zeekey85/LabStack-Rack/images/hybrid3.png

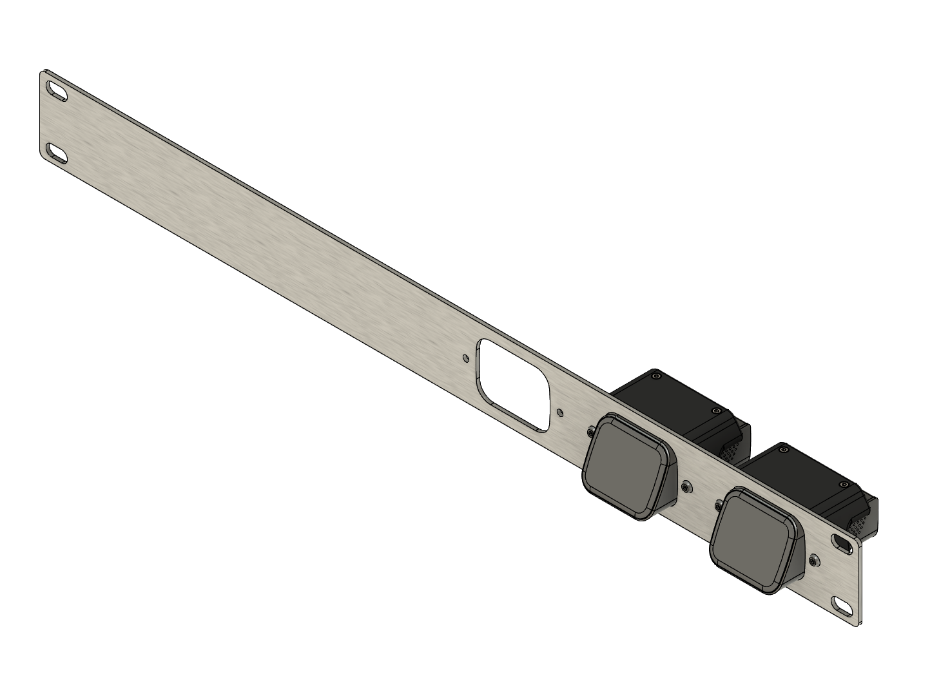
images/hybrid3.png
