zeekey85/LabStack-Rack/images/hybrid4.png

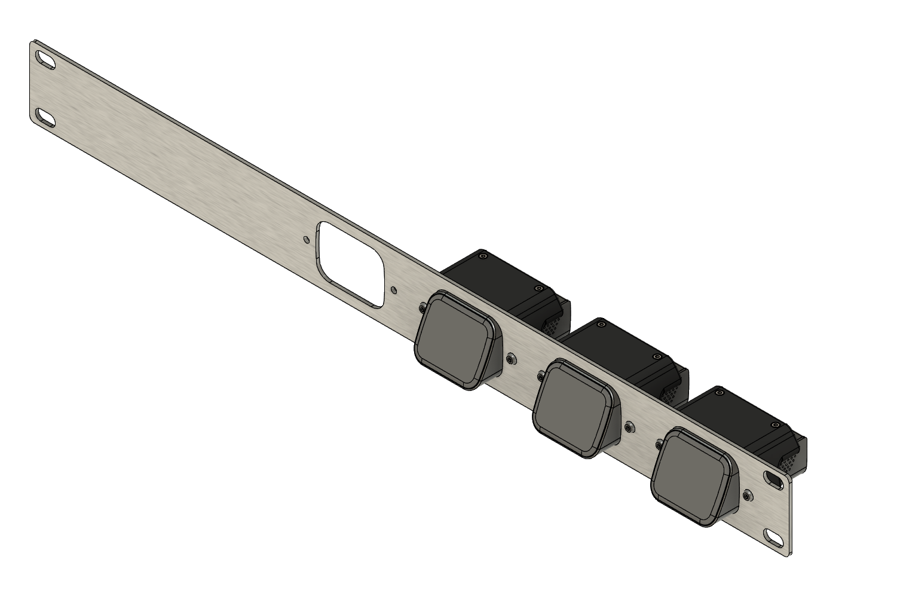
images/hybrid4.png
