zeekey85/LabStack-Rack/images/hybridshort2.png

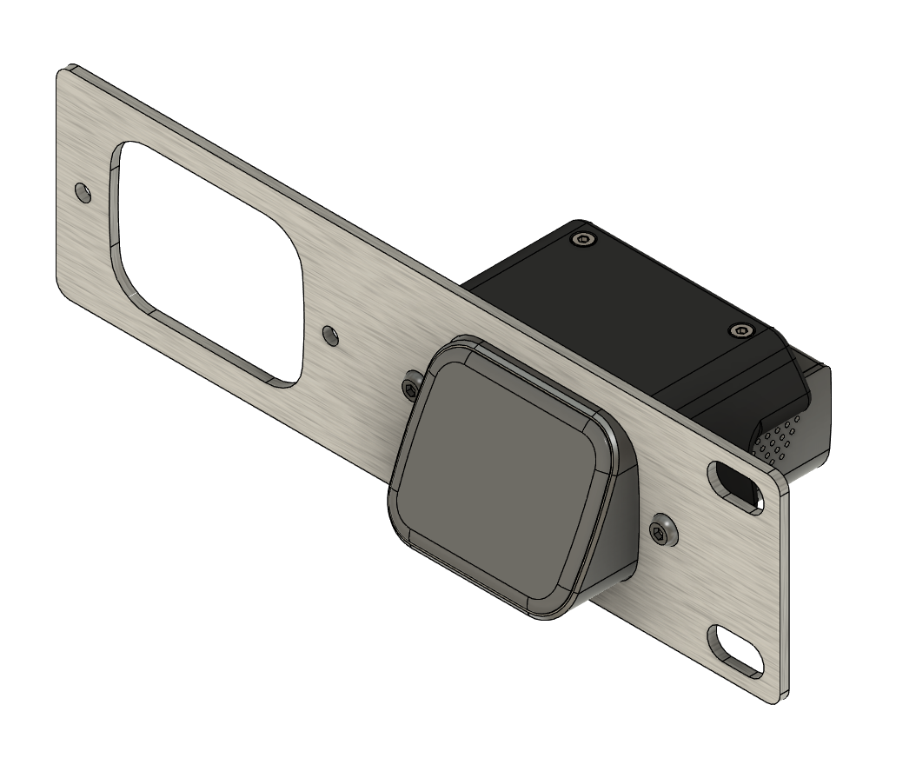
images/hybridshort2.png
