zeekey85/LabStack-Rack/LabStack Rack Mini/STLs/1U Mini Drawer Insert.stl

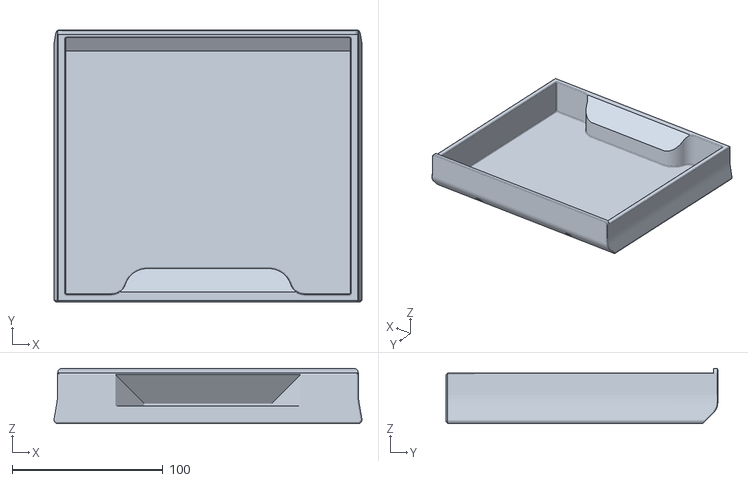
[picture p27: CAD file, 2025-01-28]
LabStack Rack Mini/STLs/1U Mini Drawer Insert.stl
204.1 x 180.0 x 36.7
