zeekey85/LabStack-Rack/full3d/1x Module 6x Keystone Left.stl

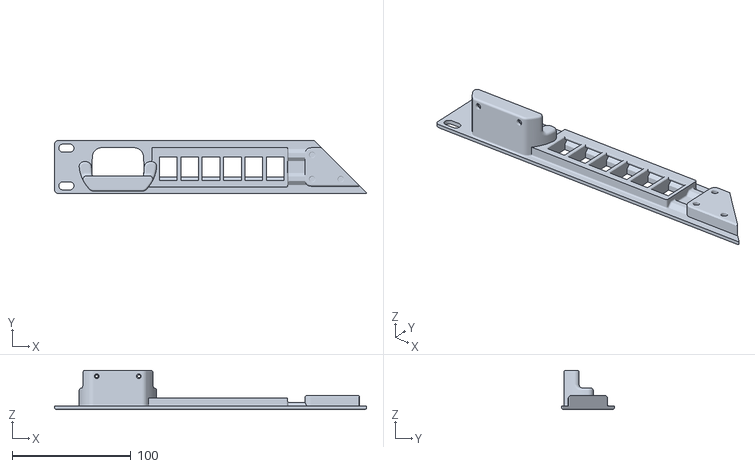
[picture p28: CAD file, 2025-01-24]
full3d/1x Module 6x Keystone Left.stl
262.8 x 44.4 x 33.2
