zeekey85/LabStack-Rack/hybrid/JetKVM 1U 2-Module.dxf

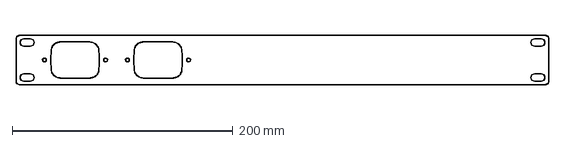
[picture p29: CAD file, 2024-12-10]
hybrid/JetKVM 1U 2-Module.dxf
482.6 x 44.5 mm
