zeekey85/LabStack-Rack/LabStack Rack Mini/STLs/1U Mini HomeAssistant Yellow.stl

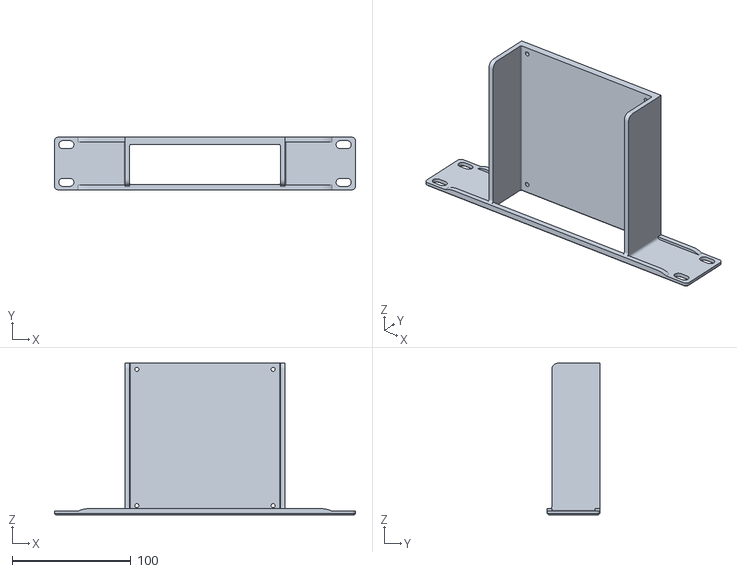
[picture p30: CAD file, 2025-01-26]
LabStack Rack Mini/STLs/1U Mini HomeAssistant Yellow.stl
254.0 x 44.4 x 128.0
