zeekey85/LabStack-Rack/LabStack Rack Mini/STLs/1U Mini Add HomeAssistant Yellow Spacer x4.stl

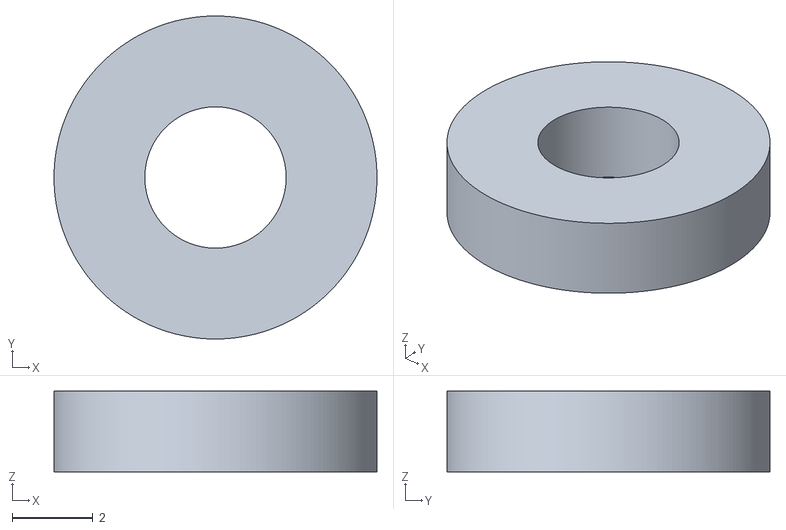
[picture p32: CAD file, 2025-01-26]
LabStack Rack Mini/STLs/1U Mini Add HomeAssistant Yellow Spacer x4.stl
8.00 x 8.00 x 2.00
