zeekey85/LabStack-Rack/full3d/2x Modules Short Right Mount.stl

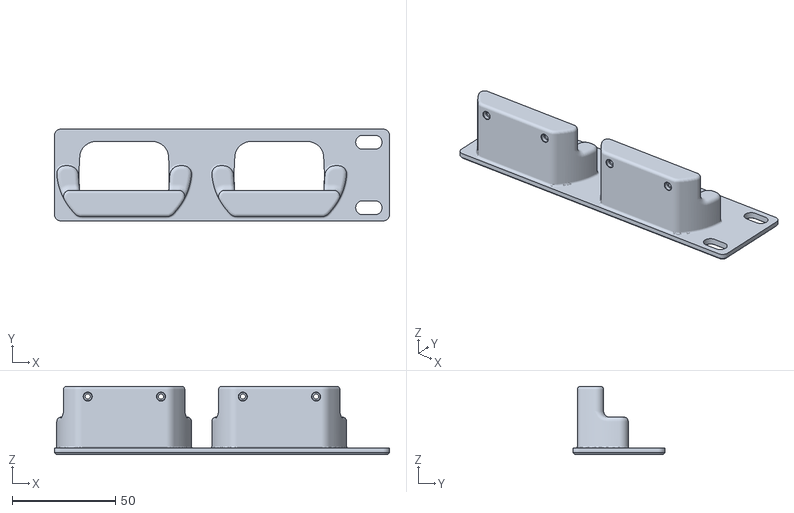
[picture p33: CAD file, 2025-01-09]
full3d/2x Modules Short Right Mount.stl
162.3 x 44.4 x 33.2
