zeekey85/LabStack-Rack/LabStack Rack Mini/STLs/1U Mini Drawer Base.stl

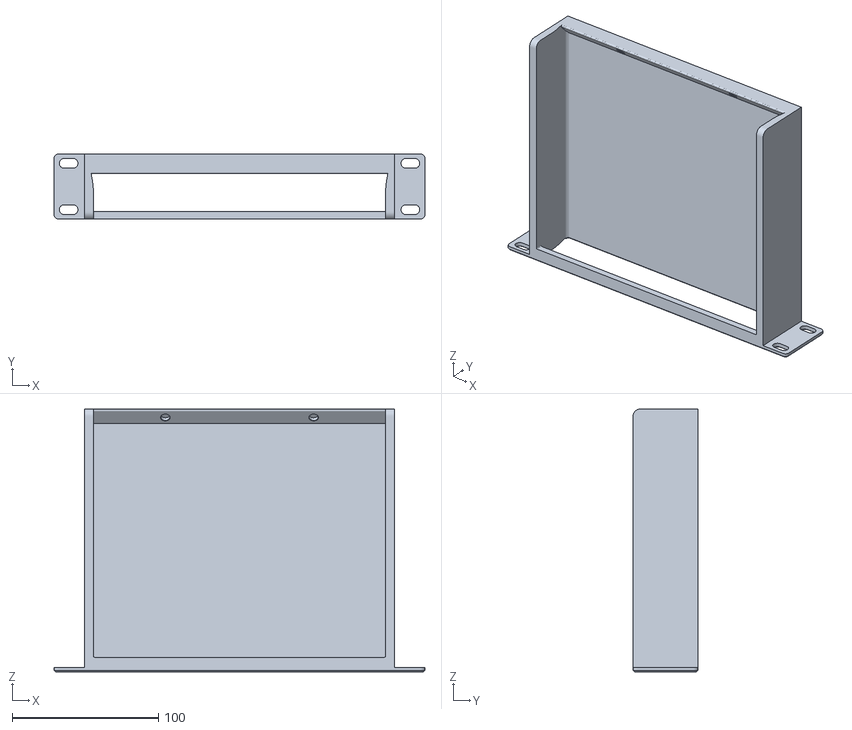
[picture p35: CAD file, 2025-01-26]
LabStack Rack Mini/STLs/1U Mini Drawer Base.stl
254.0 x 44.4 x 180.0
