zeekey85/LabStack-Rack/full3d/1x Module Right.stl

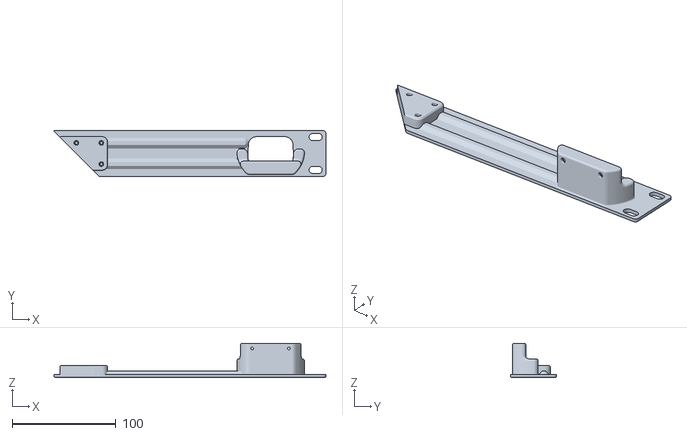
[picture p36: CAD file, 2024-12-17]
full3d/1x Module Right.stl
262.8 x 44.4 x 33.2
