zeekey85/LabStack-Rack/hybrid/JetKVM 1U 1-Module Short.dxf

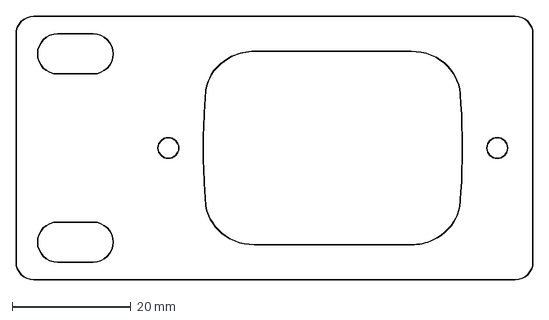
[picture p37: CAD file, 2024-12-10]
hybrid/JetKVM 1U 1-Module Short.dxf
87.2 x 44.5 mm
