zeekey85/LabStack-Rack/full3d/1x Module Short Left Mount.stl

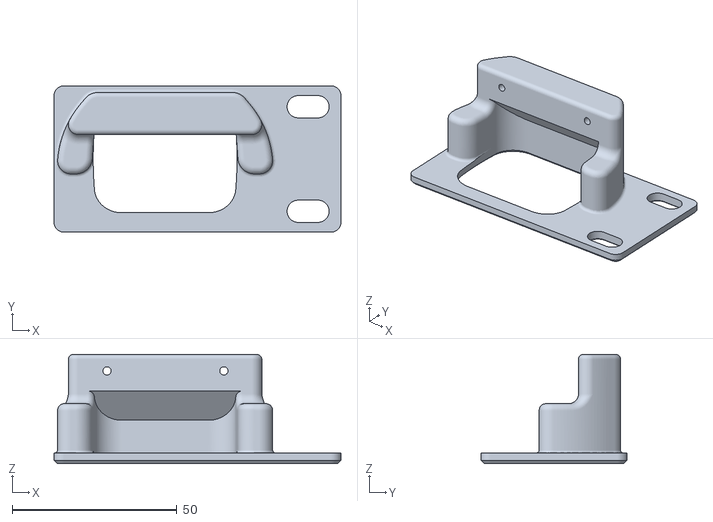
[picture p38: CAD file, 2024-12-17]
full3d/1x Module Short Left Mount.stl
87.2 x 44.5 x 33.2
