zeekey85/LabStack-Rack/hybrid/JetKVM 1U 3-Module.dxf

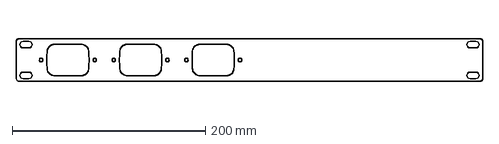
[picture p40: CAD file, 2024-12-10]
hybrid/JetKVM 1U 3-Module.dxf
482.6 x 44.5 mm
