zeekey85/LabStack-Rack/hybrid/JetKVM 1U 2-Module Short.dxf

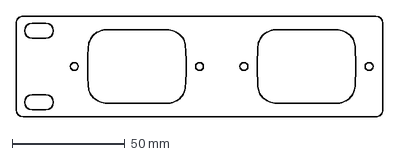
[picture p41: CAD file, 2024-12-10]
hybrid/JetKVM 1U 2-Module Short.dxf
162.3 x 44.5 mm
