zeekey85/LabStack-Rack/full3d/3x Modules 10in Single.stl

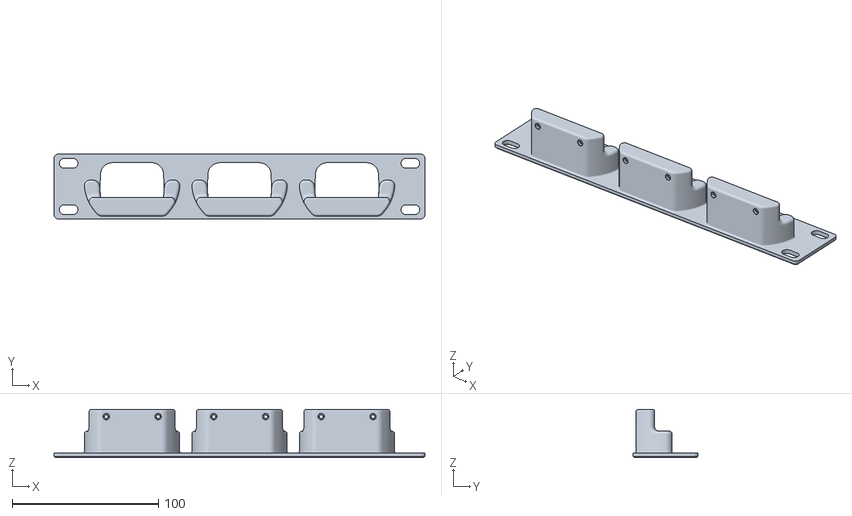
[picture p42: CAD file, 2024-12-17]
full3d/3x Modules 10in Single.stl
254.0 x 44.4 x 33.2
