zeekey85/LabStack-Rack/full3d/Brace.stl

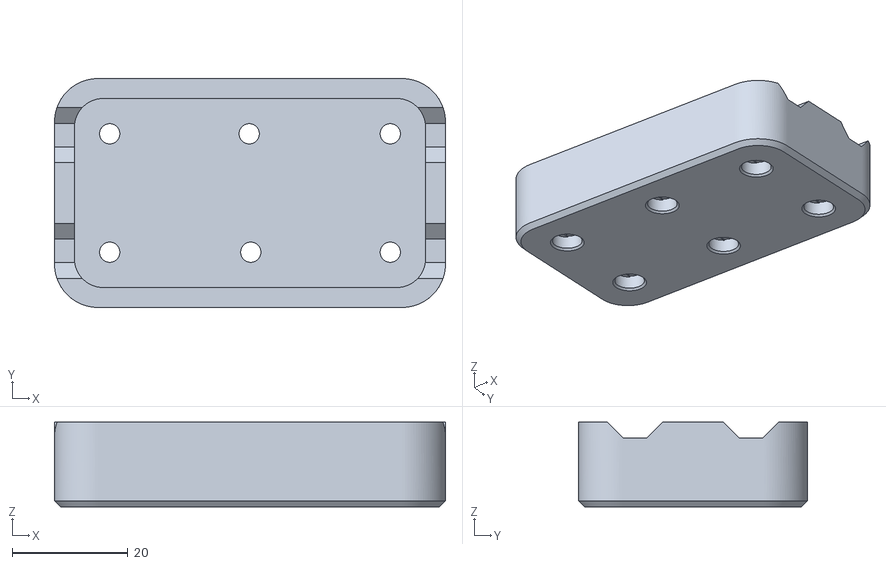
[picture p43: CAD file, 2024-12-17]
full3d/Brace.stl
67.5 x 39.5 x 14.6
