zeekey85/LabStack-Rack/full3d/Blank Module Right.stl

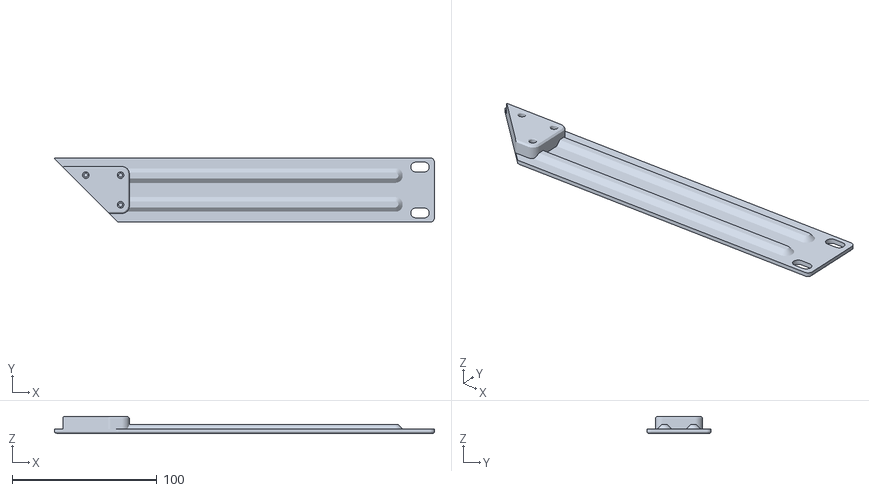
[picture p44: CAD file, 2024-12-17]
full3d/Blank Module Right.stl
262.8 x 44.4 x 11.8
